whowechina/chu_pico/Production/CAD/chu_pico_ir_cover.dxf

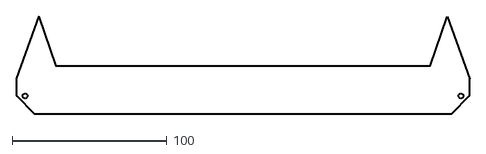
[picture p41: CAD file, 2023-09-10]
Production/CAD/chu_pico_ir_cover.dxf
293.2 x 63.3
