whowechina/chu_pico/PCB/main/3dmodels/User Library-WS2812-4020.step

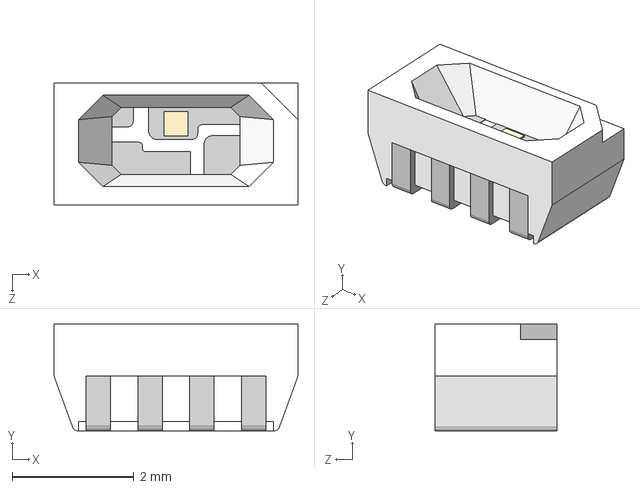
[picture p42: CAD file, 2023-08-09]
PCB/main/3dmodels/User Library-WS2812-4020.step
4.00 x 1.75 x 2.00 mm
