whowechina/chu_pico/PCB/main/3dmodels/WS2812-2020.STEP

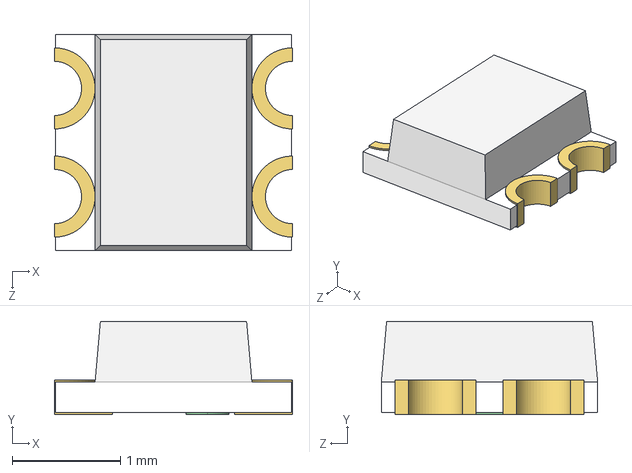
[picture p44: CAD file, 2023-08-09]
PCB/main/3dmodels/WS2812-2020.STEP
2.20 x 0.86 x 2.00 mm
