whowechina/chu_pico/PCB/main/3dmodels/WS2812B.step

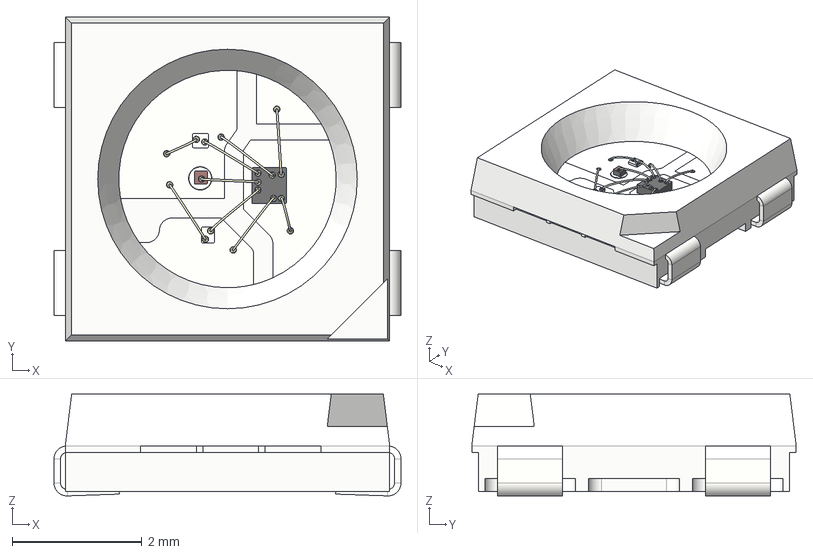
[picture p46: CAD file, 2023-08-09]
PCB/main/3dmodels/WS2812B.step
5.35 x 5.00 x 1.57 mm
