whowechina/chu_pico/PCB/main/3dmodels/SW_Hotswap_Kailh_Choc_V1.stp

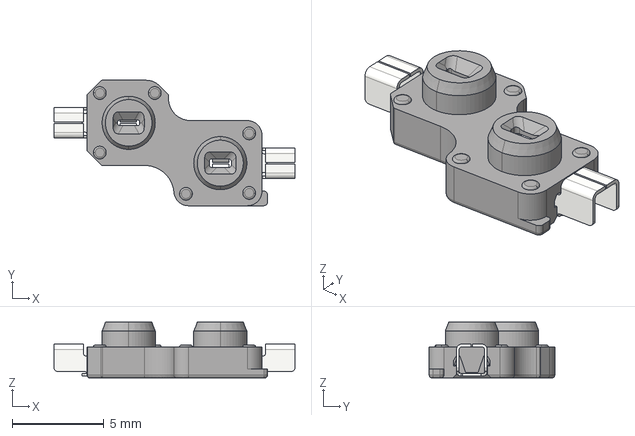
[picture p47: CAD file, 2023-08-09]
PCB/main/3dmodels/SW_Hotswap_Kailh_Choc_V1.stp
13.2 x 6.85 x 3.05 mm
