whowechina/chu_pico/PCB/main/3dmodels/User Library-PTS645SL95SMTR92-LFS.STEP

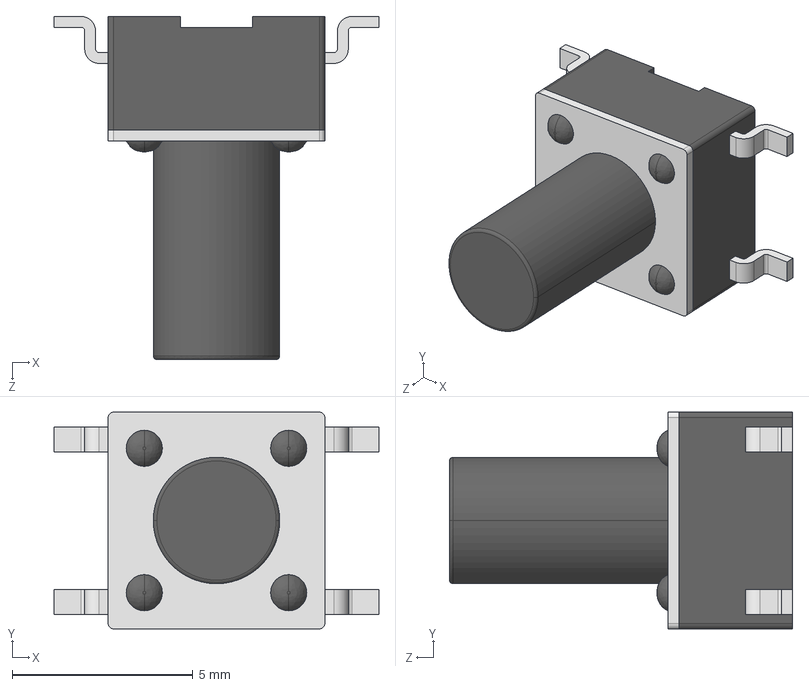
[picture p48: CAD file, 2023-08-09]
PCB/main/3dmodels/User Library-PTS645SL95SMTR92-LFS.STEP
9.00 x 6.00 x 9.50 mm
