whowechina/chu_pico/PCB/main/3dmodels/User Library-WS2812-2020.step

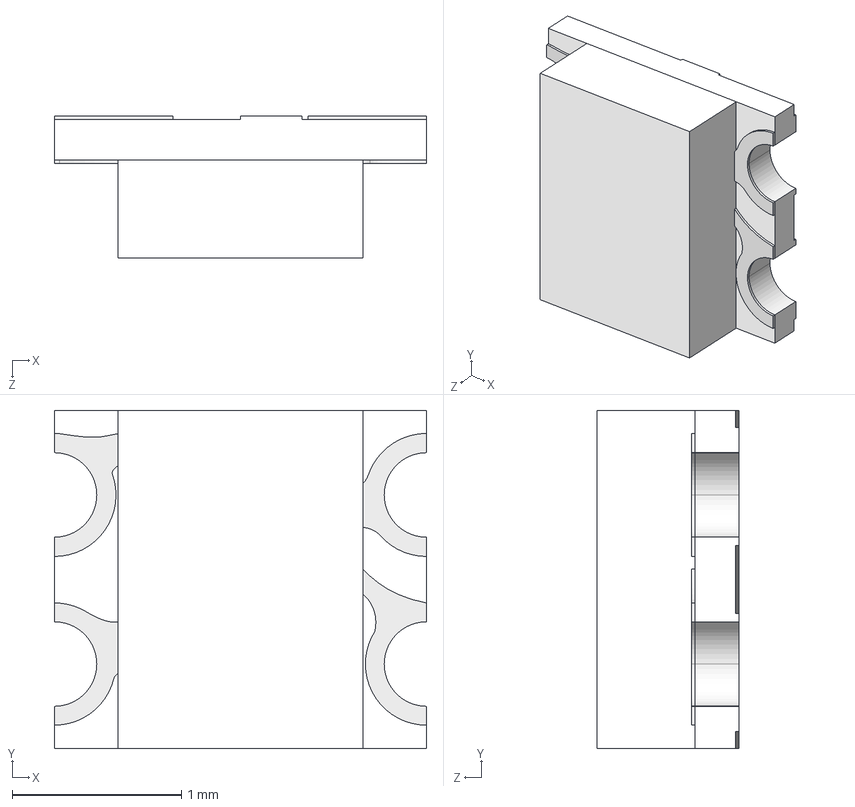
[picture p49: CAD file, 2023-08-09]
PCB/main/3dmodels/User Library-WS2812-2020.step
2.20 x 2.00 x 0.84 mm
