whowechina/chu_pico/PCB/main/3dmodels/Magnetic Pogo Connector 5 Pin (M) - 副本.STEP

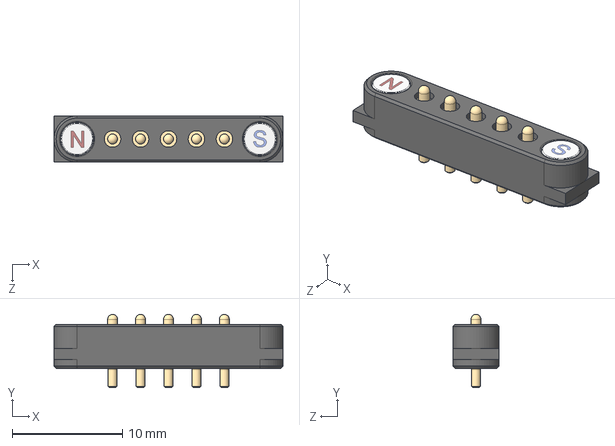
[picture p50: CAD file, 2023-08-09]
PCB/main/3dmodels/Magnetic Pogo Connector 5 Pin (M) - 副本.STEP
20.8 x 6.65 x 4.20 mm
