whowechina/chu_pico/PCB/main/3dmodels/WS2812-0807.STEP

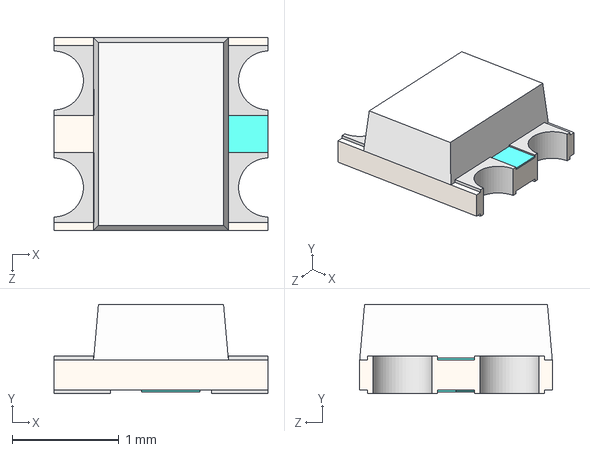
[picture p51: CAD file, 2023-08-09]
PCB/main/3dmodels/WS2812-0807.STEP
2.00 x 0.835 x 1.80 mm
