whowechina/chu_pico/PCB/main/3dmodels/Tact Switch 4.5mm SMT.step

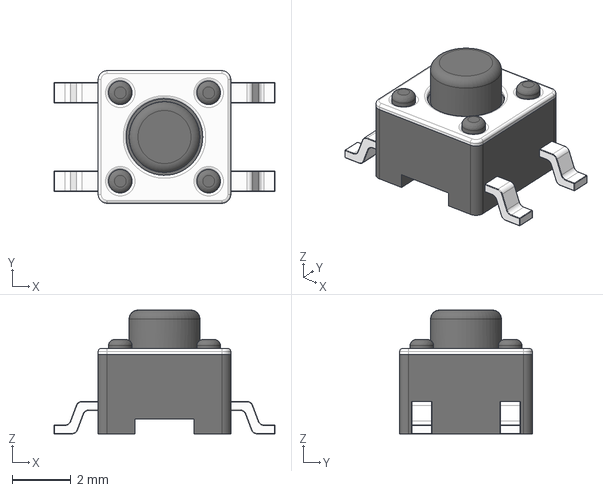
[picture p52: CAD file, 2023-08-09]
PCB/main/3dmodels/Tact Switch 4.5mm SMT.step
7.50 x 4.50 x 4.20 mm
