whowechina/chu_pico/PCB/main/3dmodels/Kailh LP Choc PC Keycap.step

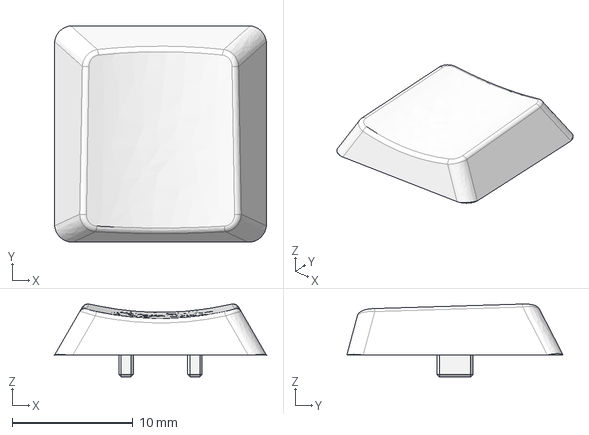
[picture p55: CAD file, 2023-08-09]
PCB/main/3dmodels/Kailh LP Choc PC Keycap.step
17.5 x 17.9 x 6.03 mm
