whowechina/chu_pico/PCB/main/3dmodels/SW_Kailh_Choc_V1.stp

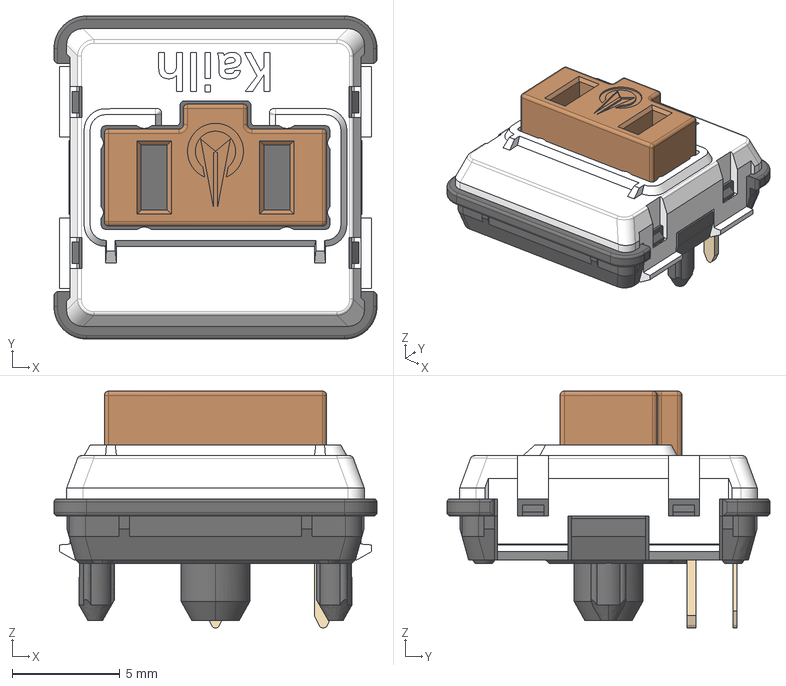
[picture p56: CAD file, 2023-08-09]
PCB/main/3dmodels/SW_Kailh_Choc_V1.stp
15.0 x 15.0 x 11.0 mm
