whowechina/chu_pico/PCB/main/3dmodels/J 2835.step

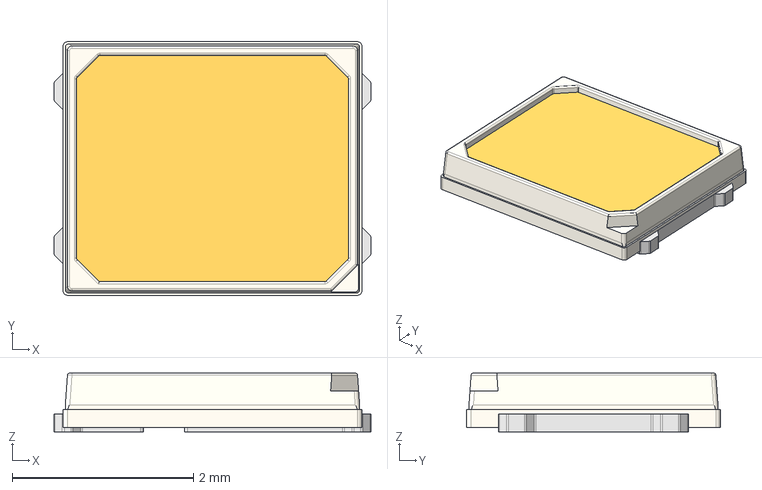
[picture p57: CAD file, 2023-08-09]
PCB/main/3dmodels/J 2835.step
3.50 x 2.80 x 0.65 mm
